BlackBrix/USB_Helper/enclosure V2/USB_enclosure_V2_Exo_Square_3.png

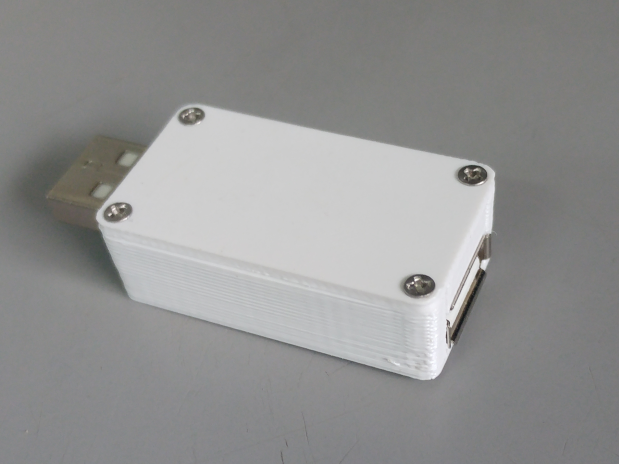
enclosure V2/USB_enclosure_V2_Exo_Square_3.png
