BlackBrix/USB_Helper/photos/IMG_9731.JPG

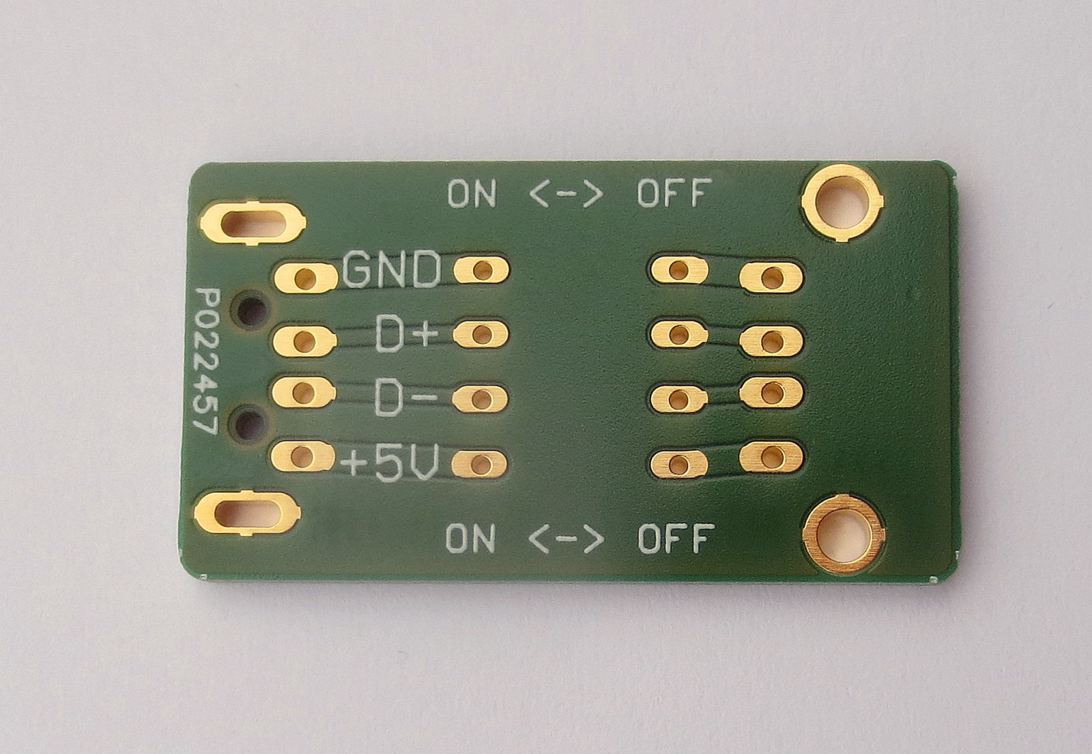
photos/IMG_9731.JPG
