BlackBrix/USB_Helper/photos/IMG_9732.JPG

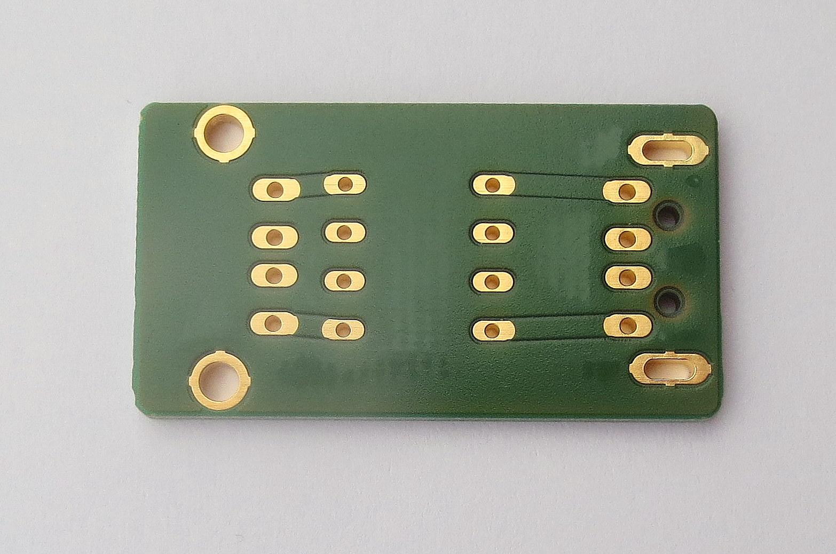
photos/IMG_9732.JPG
