BlackBrix/USB_Helper/photos/IMG_9736.JPG

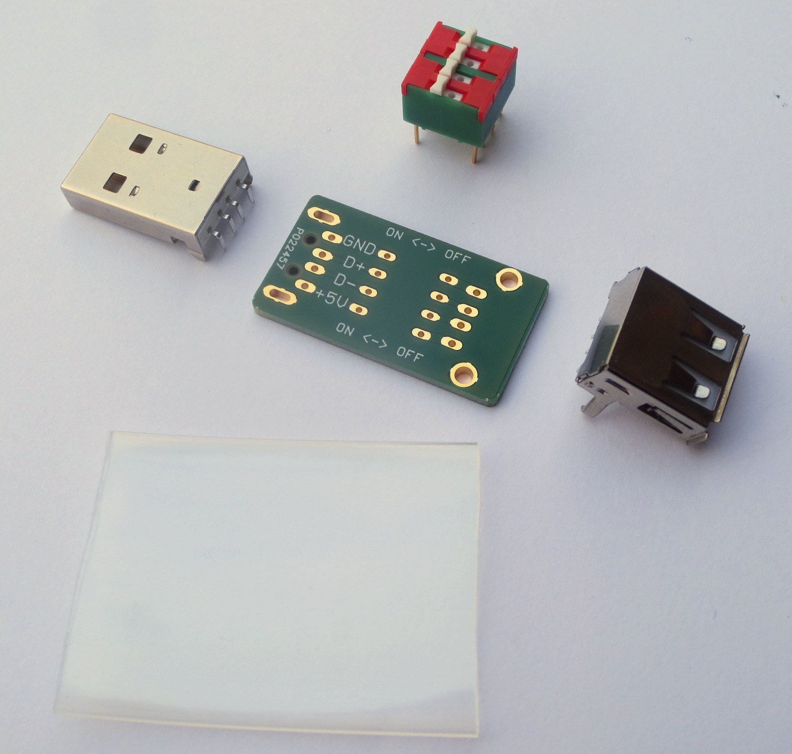
photos/IMG_9736.JPG
