BlackBrix/USB_Helper/photos/IMG_9737.JPG

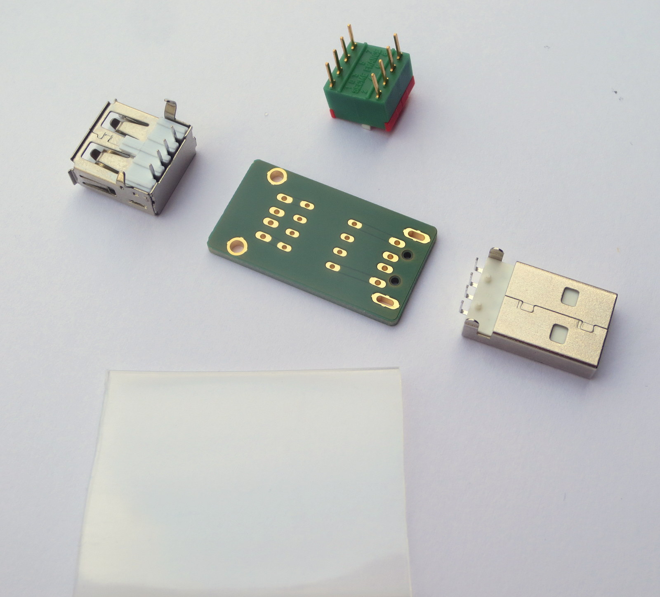
photos/IMG_9737.JPG
