BlackBrix/USB_Helper/photos/IMG_9741.JPG

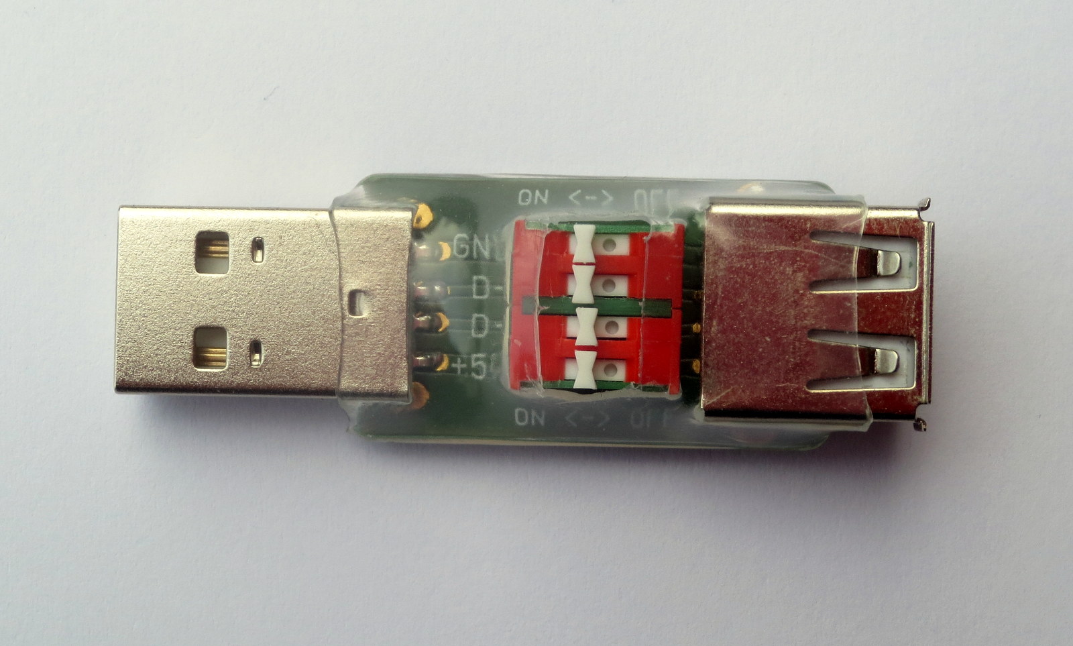
photos/IMG_9741.JPG
