BlackBrix/USB_Helper/photos/IMG_9742.JPG

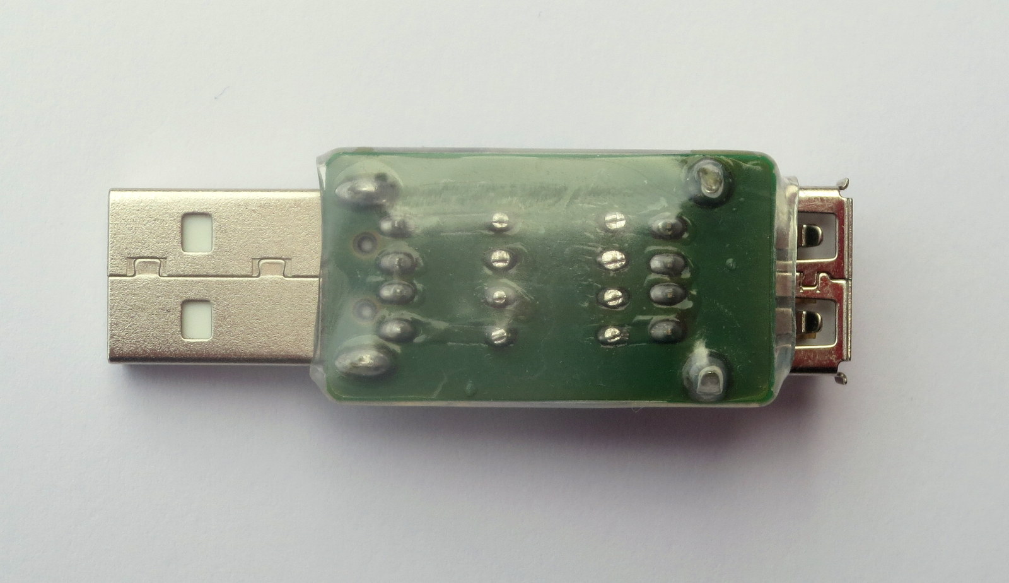
photos/IMG_9742.JPG
