BlackBrix/USB_Helper/photos/IMG_9743.JPG

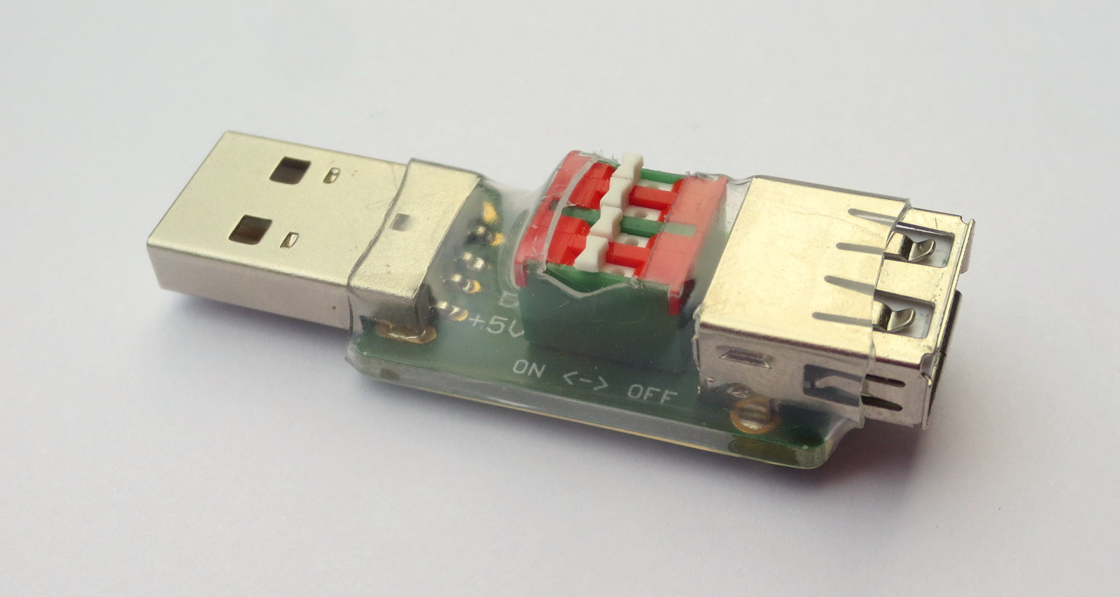
photos/IMG_9743.JPG
