BlackBrix/USB_Helper/photos/IMG_9745.JPG

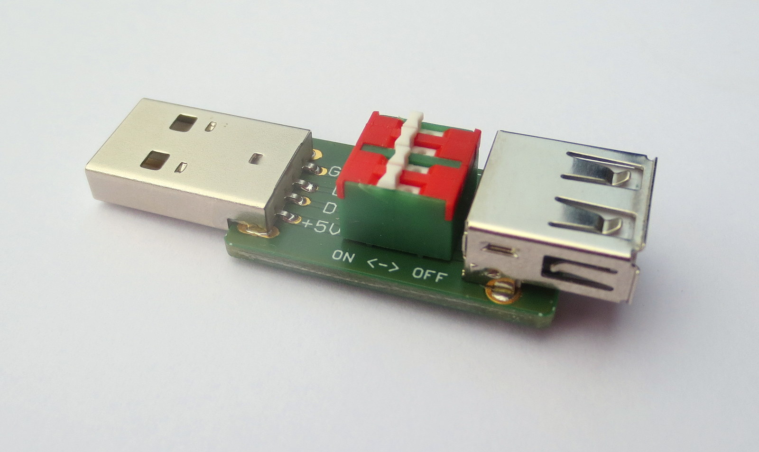
photos/IMG_9745.JPG
