BlackBrix/USB_Helper/photos/IMG_9746.JPG

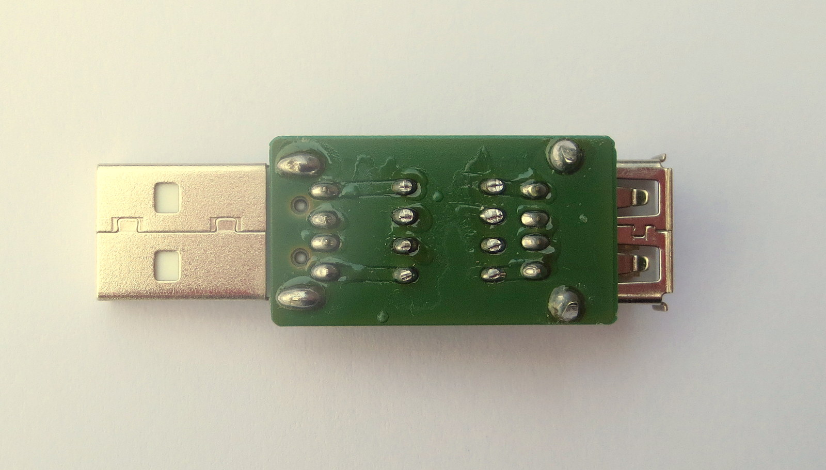
photos/IMG_9746.JPG
