BlackBrix/USB_Helper/photos/IMG_9748.JPG

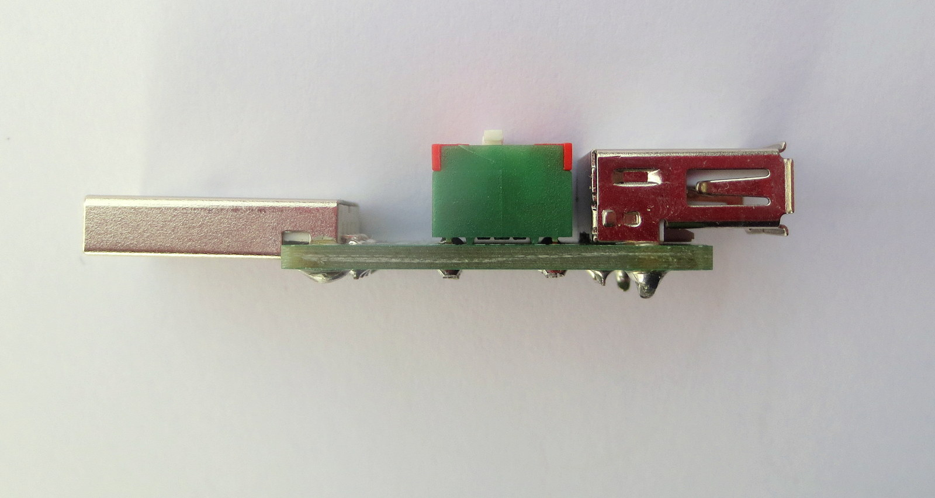
photos/IMG_9748.JPG
